Rimebeck/CLEAVE-HHJP/build-guide/images/assembly/continuity-test/diode.jpg

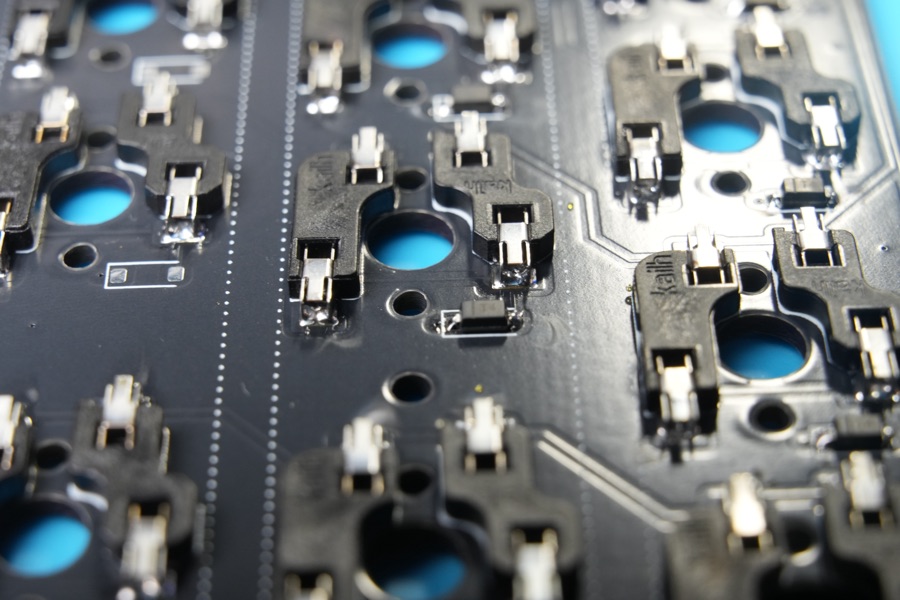
build-guide/images/assembly/continuity-test/diode.jpg
